LoicM22/Tetris_project/Tetris_projet/cahier_des_charges_tetris_projet.pdf

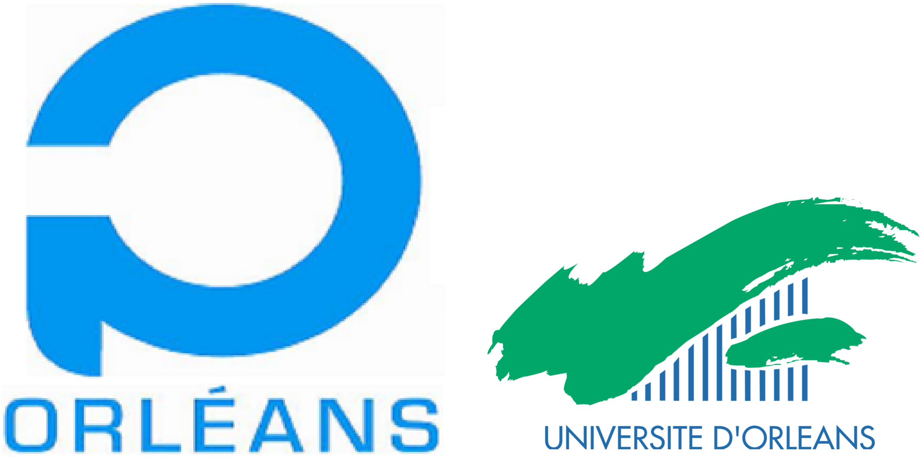
[picture p60: figure]

# Cahier des charges

# Projet Tetris

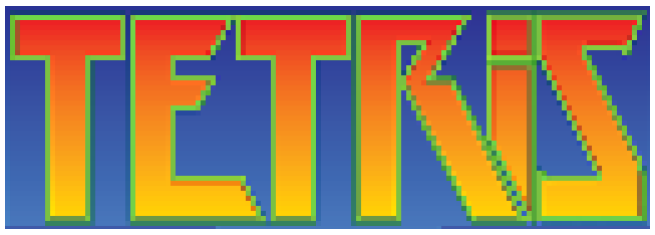
[picture p61: figure]

Polytech Orléans | Cahier des charges | 2021 / 2022

# 1.But du projet

Offirir une nouvelle expérience pour les joueurs de Tetris. En effet, actuellement on

utilisesoit des joysticks soit des flèches directionnelles pour pouvoir agir sur le jeu en

question.

Le but de ce projet est donc de pouvoir jouer à Tetris en utilisant une commande à

distance que l’on inclinerait en fonction de comment nous voudrion tourner la pièce de

Tetris.

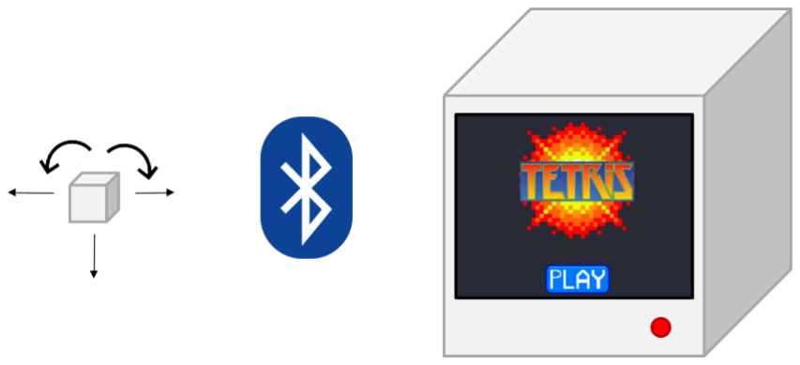
[picture p62: figure]

Figure 1.1 – Schéma récapitulatif du projet

Loïc Marchand | Tetris | 1

Polytech Orléans | Cahier des charges | 2021 / 2022

# 2.Bête à cornes

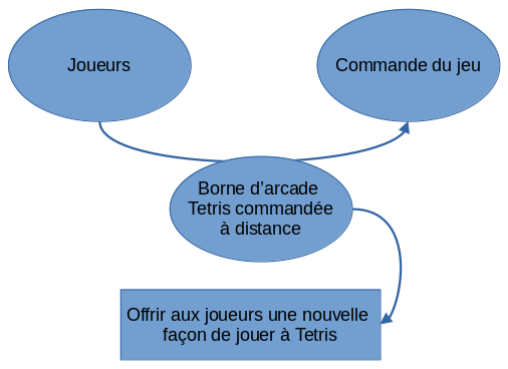
[picture p63: figure]

Figure 2.1 – Bête à cornes

Loïc Marchand | Tetris | 2

Polytech Orléans | Cahier des charges | 2021 / 2022

# 3.CQQCOQP

Comment ?

En utilisant les connaissances accumulées jusqu’à maintenant, mais également toutes

les ressources qui sont à ma disposition. Ce projet sera fait avec, comme support, une

Raspberry Pi.

Qui ?

Ce projet sera réalisé par moi-même et encadré par un professeur tuteur. Il vise les

personnes aimant jouer à Tetris.

Quoi ?

Une borne d’arcade Tetris controlable à distance par une télécommande en forme de

cube qu’il faudra incliner et translater pour faire bouger les pièces de Tetris à l’écran.

Combien ?

Une télécommande cubique avec une borne d’arcade.

Où ?

À Polytech Orléans.

Quand ?

Á partir du 01 Octobre juqu’à courant Janvier.

Pourquoi ?

Avoir une nouvelle façon de jouer à Tetris.

Polytech Orléans | Cahier des charges | 2021 / 2022

# 4.Diagramme pieuvre

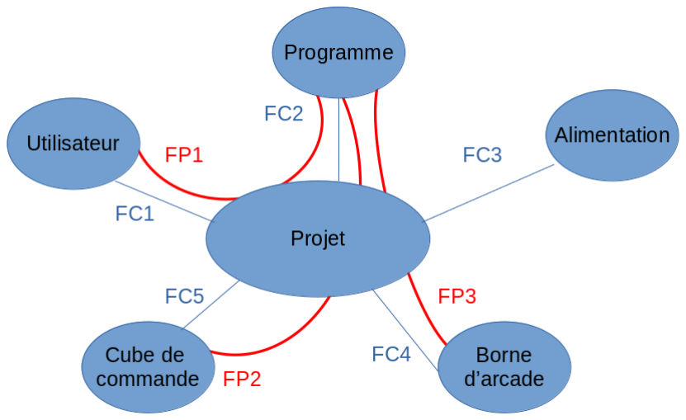
[picture p64: figure]

Figure 4.1 – Diagramme pieuvre

Polytech Orléans | Cahier des charges | 2021 / 2022

# 5.Liste des fonctions

Id | Fonctions | Précisions | Critères | Solutions
FP1 | Permettre à l’utilisateur de jouer au jeu Tetris
FP1.1 | | Interface simple d’utilisation | Utilisable par un enfant de plus de 3 ans
FP2 | Avoir un cube qui permet de commander à distance le Te-tris gràce aux mouvements
FP2.1 | | Cube comman-dable sans fil | Distance : 2m | Bluetooth
FP2.2 | | Cube rechar-geable | Temps d’uti-lisation : 1h et Temps de recharge : 30min
FP2.3 | | Facilement utili-sable | Utilisable par un enfant de 3ans

FP2.4 | | Doit être résis-tant aux chutes | Hauteur : 2m
FP2.5 | | Visuellement joli | | LED et miroirs
FP3 | Jouer à Tetris sur une borne d’arcade
FP3.1 | | Bonne qualité | Poids : 8kg et Temps de réac-tion : <25ms
FP3.2 | | Interaction avec le jeu | Effet lumineux
FC1 | Etre intuitif | | Des contrôles simples
FC2 | Programme Py-thon modulable | | Pouvoir mettre toutes les inté-ractions que l’on veut
FC3 | Borne fonc-tionne sur secteur | | Alimentation 230V
FC4 | Fournir un son et une image nets | | Ampli + ecran
FC5 | Petit cube ergo-nomique | | Poids <500g

6

Polytech Orléans | Cahier des charges | 2021 / 2022

# 6.Analyse de risque

NOM | Fréquence | Urgence | Criticité | Plans d’action
Délai de livrai-son | 2 | 4 | 8 | Prévoir des tâches ne né-cessitant pas de matériel particulier

# 7.GANTT

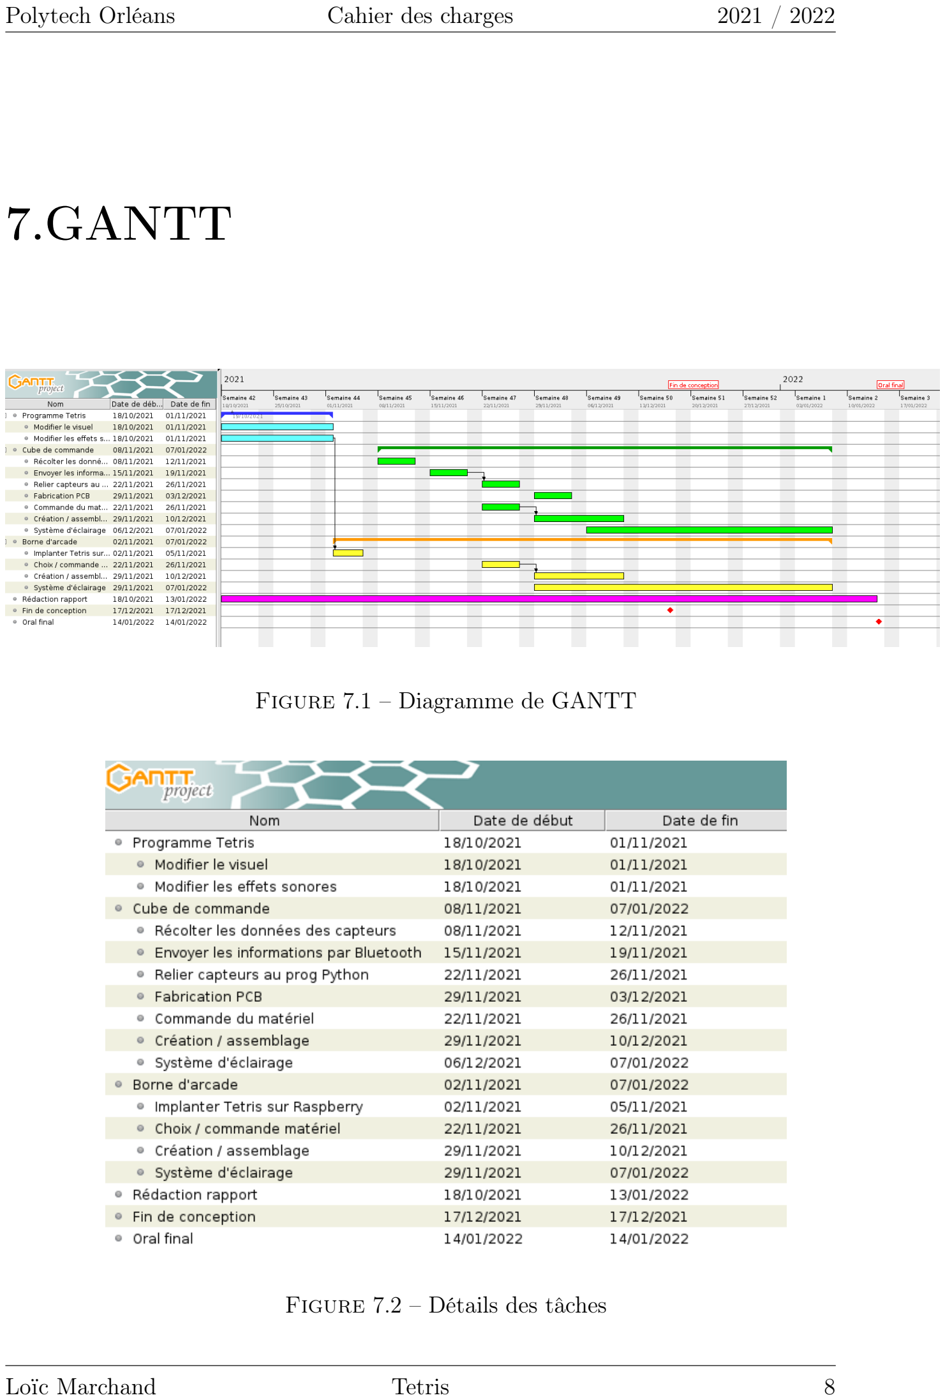
[picture p65: page 9]

Polytech Orléans | Cahier des charges | 2021 / 2022

Figure 7.1 – Diagramme de GANTT

Figure 7.2 – Détails des tâches
